eriknl1982/Doorbell_modernizr/arduino sample code/For v2.0/WifiManager sample/logo.H

const uint8_t Logo_bits[] PROGMEM = {

 0x00, 0x00, 0x00, 0x00, 0x00, 0x00, 0x00, 0x00, 0x00, 0x00, 0x00, 0x00,
  0x00, 0x00, 0x00, 0x00, 0x00, 0x00, 0x00, 0x00, 0xE0, 0xFF, 0x03, 0x00,
  0x00, 0x00, 0x00, 0x00, 0x78, 0x00, 0x3F, 0x00, 0x00, 0x00, 0x00, 0x00,
  0x0F, 0x00, 0xFC, 0x00, 0x00, 0x00, 0x00, 0xC0, 0x03, 0x00, 0x78, 0x00,
  0x00, 0x00, 0x00, 0xF0, 0x00, 0x00, 0x00, 0x00, 0x00, 0x00, 0x00, 0x1E,
  0xC0, 0xFF, 0x03, 0x00, 0x00, 0xFF, 0xFF, 0x07, 0xFC, 0xFF, 0x3F, 0x00,
  0x00, 0x03, 0x00, 0x07, 0xFF, 0xFF, 0xFF, 0x00, 0x80, 0x03, 0x00, 0xC6,
  0xFF, 0xFF, 0xFF, 0x03, 0x80, 0x03, 0x00, 0xF3, 0xFF, 0xFF, 0xFF, 0x0F,
  0x80, 0x03, 0x80, 0xF9, 0xFF, 0xFF, 0xFF, 0x1F, 0x80, 0x03, 0xC0, 0xFC,
  0xFF, 0xFF, 0xFF, 0x3F, 0x80, 0x03, 0xE0, 0xFC, 0xFF, 0xC3, 0xFF, 0x3F,
  0x80, 0x03, 0x60, 0xFE, 0x7F, 0x00, 0xFE, 0x7F, 0x80, 0x03, 0x60, 0xFE,
  0x3F, 0x7E, 0xFC, 0x7F, 0x80, 0x03, 0x60, 0xCE, 0x3F, 0xFF, 0xFC, 0x7F,
  0x80, 0x03, 0x60, 0xCE, 0x3F, 0xFF, 0xFC, 0x7F, 0x80, 0x03, 0x60, 0xCE,
  0x3F, 0x7E, 0xFC, 0x7F, 0x80, 0x03, 0x60, 0x9E, 0xFF, 0x00, 0xFF, 0x7F,
  0x80, 0x03, 0xE0, 0x1C, 0xFF, 0xE7, 0xFF, 0x3F, 0x80, 0x03, 0xC0, 0x39,
  0xFE, 0xFF, 0xFF, 0x1F, 0x80, 0x03, 0x80, 0x71, 0xFC, 0xFF, 0xFF, 0x1F,
  0x80, 0x03, 0x00, 0xE7, 0xF1, 0xFF, 0xFF, 0x07, 0x80, 0x03, 0x00, 0xC6,
  0x87, 0xFF, 0xFF, 0x03, 0x00, 0x03, 0x00, 0x07, 0x3F, 0xE0, 0xFF, 0x00,
  0x00, 0xFE, 0xFF, 0x03, 0xF8, 0xFF, 0x3F, 0x00, 0x00, 0x00, 0x00, 0x00,
  0x80, 0xFF, 0x01, 0x00, 0x00, 0x00, 0x00, 0x00, 0x00, 0x00, 0x00, 0x00,
  0x00, 0x00, 0x00, 0x00, 0x00, 0x00, 0x00, 0x00, 0x00, 0x00, 0x00, 0x00,
  0x00, 0x00, 0x00, 0x00, 0x00, 0x00, 0x00, 0x00, 0x00, 0x00, 0x00, 0x00,
  0x00, 0x00, 0x00, 0xC0, 0xFF, 0x1F, 0xF8, 0x07, 0x00, 0x00, 0x00, 0xC0,
  0xFF, 0x1F, 0x38, 0x00, 0x00, 0x00, 0x00, 0xC0, 0x00, 0x18, 0xE0, 0x00,
  0x00, 0x00, 0x00, 0xC0, 0x00, 0x18, 0x80, 0x01, 0x00, 0x00, 0x00, 0xC0,
  0x00, 0x18, 0x80, 0x01, 0x00, 0x00, 0x00, 0xC0, 0x00, 0x18, 0xE0, 0x00,
  0x00, 0x00, 0x00, 0xC0, 0x00, 0x18, 0x38, 0x00, 0x00, 0x00, 0x00, 0xC0,
  0x01, 0x1C, 0xF8, 0x07, 0x00, 0x00, 0x00, 0x80, 0x07, 0x0E, 0x00, 0x00,
  0x00, 0x00, 0x00, 0x00, 0xFE, 0x07, 0x00, 0x00, 0x00, 0x00, 0x00, 0x00,
  0xF0, 0x00, 0x00, 0x00, 0x00, 0x00, 0x00, 0x00, 0x00, 0x00, 0x00, 0x00,
  0x00, 0x00, 0x00, 0x00, 0x00, 0x00, 0x00, 0x00, 0x00, 0x00, 0x00, 0x00,
  0xFE, 0x03, 0xF0, 0x03, 0x00, 0x00, 0x00, 0x80, 0x07, 0x0F, 0x18, 0x06,
  0x00, 0x00, 0x00, 0xC0, 0x01, 0x1C, 0x0C, 0x0C, 0x00, 0x00, 0x00, 0xC0,
  0x00, 0x18, 0x0C, 0x0C, 0x00, 0x00, 0x00, 0xC0, 0x00, 0x38, 0x0C, 0x0C,
  0x00, 0x00, 0x00, 0xC0, 0x00, 0x38, 0x3C, 0x07, 0x00, 0x00, 0x00, 0xC0,
  0x00, 0x18, 0xE0, 0x01, 0x00, 0x00, 0x00, 0xC0, 0x01, 0x1C, 0x00, 0x00,
  0x00, 0x00, 0x00, 0x80, 0x03, 0x0E, 0x00, 0x00, 0x00, 0x00, 0x00, 0x00,
  0xFF, 0x07, 0x00, 0x00, 0x00, 0x00, 0x00, 0x00, 0xF8, 0x01, 0x00, 0x00,
  0x00, 0x00, 0x00, 0x00, 0x00, 0x00, 0x00, 0x00, 0x00, 0x00, 0x00, 0x00,
  0x00, 0x00, 0xF8, 0x07, 0x00, 0x00, 0x00, 0x00, 0xFC, 0x03, 0x08, 0x0C,
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
